adafruit/Adafruit-MiniPOV4-Kit/Bootloader/main.c

/* VUSBtinyBoot by me@frank-zhao.com
 *  
 * VUSBtinyBoot is a bootloader that emulates a USBtinyISP (from Adafruit Industries)
 *  
 * MiniPOV4 (from Adafruit Industries) will use VUSBtinyBoot
 *
 * This code is heavily derived from USBaspLoader, but also from USBtiny, with USBtinyISP's settings
 
   Copyright (c) 2013 Adafruit Industries
   All rights reserved.

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
    THIS SOFTWARE IS PROVIDED BY THE COPYRIGHT HOLDERS AND CONTRIBUTORS "AS IS"
    AND ANY EXPRESS OR IMPLIED WARRANTIES, INCLUDING, BUT NOT LIMITED TO, THE
    IMPLIED WARRANTIES OF MERCHANTABILITY AND FITNESS FOR A PARTICULAR PURPOSE
    ARE DISCLAIMED. IN NO EVENT SHALL THE COPYRIGHT OWNER OR CONTRIBUTORS BE
    LIABLE FOR ANY DIRECT, INDIRECT, INCIDENTAL, SPECIAL, EXEMPLARY, OR
    CONSEQUENTIAL DAMAGES (INCLUDING, BUT NOT LIMITED TO, PROCUREMENT OF
    SUBSTITUTE GOODS OR SERVICES; LOSS OF USE, DATA, OR PROFITS; OR BUSINESS
    INTERRUPTION) HOWEVER CAUSED AND ON ANY THEORY OF LIABILITY, WHETHER IN
    CONTRACT, STRICT LIABILITY, OR TORT (INCLUDING NEGLIGENCE OR OTHERWISE)
    ARISING IN ANY WAY OUT OF THE USE OF THIS SOFTWARE, EVEN IF ADVISED OF THE
    POSSIBILITY OF SUCH DAMAGE.
 */

#include <avr/io.h>
#ifndef MCUSR
#define MCUSR MCUCSR // hack for enabling ATmega8 support
#endif
#define	SIGRD	5	// this is missing from some of the io.h files, this is a hack so avr/boot.h can be used
#include <avr/boot.h>
#include <avr/pgmspace.h>
//#include <avr/fuse.h>
#include <avr/interrupt.h>
#include <avr/wdt.h>
//#include <util/delay.h>
#include <bootloaderconfig.h>
#include <usbdrv/usbdrv.c>	// must be included, because of static function declarations are being used, which saves flash space

// enable features here
#define ENABLE_FLASH_WRITING
#define ENABLE_FLASH_READING
#define ENABLE_EEPROM_WRITING
#define ENABLE_EEPROM_READING
#define ENABLE_SIG_READING
//#define ENABLE_FUSE_READING
#define ENABLE_REQUEST_EXIT // note: enabling this actually decreases code size
#define ENABLE_CLEAN_EXIT // must be used with ENABLE_REQUEST_EXIT

enum
{
	// Generic requests
	USBTINY_ECHO,		// echo test
	USBTINY_READ,		// read byte
	USBTINY_WRITE,		// write byte
	USBTINY_CLR,		// clear bit 
	USBTINY_SET,		// set bit
	// Programming requests
	USBTINY_POWERUP,	// apply power (wValue:SCK-period, wIndex:RESET)
	USBTINY_POWERDOWN,	// remove power from chip
	USBTINY_SPI,		// issue SPI command (wValue:c1c0, wIndex:c3c2)
	USBTINY_POLL_BYTES,	// set poll bytes for write (wValue:p1p2)
	USBTINY_FLASH_READ,	// read flash (wIndex:address)
	USBTINY_FLASH_WRITE,	// write flash (wIndex:address, wValue:timeout)
	USBTINY_EEPROM_READ,	// read eeprom (wIndex:address)
	USBTINY_EEPROM_WRITE,	// write eeprom (wIndex:address, wValue:timeout)
	USBTINY_DDRWRITE,		// set port direction
	USBTINY_SPI1			// a single SPI command
};

#if (FLASHEND) > 0xFFFF		// need long addressing for large flash
#	define CUR_ADDR			cur_addr.addr
#	define addr_t			uint32_t
#else
#	define CUR_ADDR			cur_addr.u16[0]
#	define addr_t			uint16_t
#endif

typedef union longConverter { // utility for manipulating address pointer with proper endianness
	addr_t		addr;
	uint16_t	u16[sizeof(addr_t)/2];
	uint8_t		u8[sizeof(addr_t)];
} longConverter_t;

#ifdef ENABLE_REQUEST_EXIT
static	uint8_t				req_boot_exit;
#endif
static	longConverter_t		cur_addr;
static	uchar				dirty = 0;			// if flash needs to be written
static	uchar				cmd0;				// current read/write command byte
static	uint8_t				remaining;			// bytes remaining in current transaction
static	uchar				buffer[8];			// talk via setup
volatile char				usbHasRxed = 0;		// whether or not USB comm is active

void (*app_start)(void) = 0x0000; // function at start of flash memory, call to exit bootloader

// ----------------------------------------------------------------------
// finishes a write operation if already started
// ----------------------------------------------------------------------
static void finalize_flash_if_dirty()
{
	if (dirty != 0)
	{
		#ifdef ENABLE_FLASH_WRITING
		cli();
		boot_page_write(CUR_ADDR - 2);
		sei();
		boot_spm_busy_wait();
		cli();
		boot_rww_enable();
		sei();
		#endif
		dirty = 0;
	}
}

// ----------------------------------------------------------------------
// Handle a non-standard SETUP packet.
// ----------------------------------------------------------------------
uchar	usbFunctionSetup ( uchar data[8] )
{
	uchar	req;
	usbRequest_t *rq = (void *)data;

	// Generic requests
	req = data[1];
	if ( req == USBTINY_ECHO )
	{
		//usbMsgPtr = data;
		return 8;
	}
	/*
	else if ( req == USBTINY_SET || req == USBTINY_CLR || req == USBTINY_WRITE || req == USBTINY_DDRWRITE || req == USBTINY_POWERUP) {
		// do nothing
		return 0;
	}
	//*/
	else if ( req == USBTINY_READ) {
		// do nothing
		return 1;
	}
	else if ( req == USBTINY_POWERDOWN )
	{
		finalize_flash_if_dirty();
		#ifdef ENABLE_REQUEST_EXIT
		req_boot_exit = 1;
		#endif
		return 0;
	}
	else if ( req == USBTINY_SPI )
	{
		finalize_flash_if_dirty(); // partial page writes are not fully written unless this is called here, it must be HERE

		usbMsgPtr = (usbMsgPtr_t)buffer;

		// this tricks "usbtiny_cmd" into succeeding
		buffer[2] = data[3];

		// for the commands, refer to ATmega datasheet under "Serial Programming Instruction Set"
		// usage of avr/boot.h here is experimental

		#ifdef ENABLE_SIG_READING
		if (data[2] == 0x30 && data[3] == 0x00) {
			// read signature byte
			buffer[3] = boot_signature_byte_get(data[4] * 2);
		}
		#ifndef ENABLE_FUSE_READING
		else
		{
			buffer[3] = 0;
		}
		#endif
		#endif
		#ifdef ENABLE_FUSE_READING
		if (data[2] == 0x50 && data[3] == 0x00 && data[4] == 0x00) {
			// read LFUSE
			buffer[3] = boot_lock_fuse_bits_get(GET_LOW_FUSE_BITS);
		}
		else if (data[2] == 0x58 && data[3] == 0x08 && data[4] == 0x00) {
			// read HFUSE
			buffer[3] = boot_lock_fuse_bits_get(GET_HIGH_FUSE_BITS);
		}
		else if (data[2] == 0x50 && data[3] == 0x08 && data[4] == 0x00) {
			// read EFUSE
			buffer[3] = boot_lock_fuse_bits_get(GET_EXTENDED_FUSE_BITS);
		}
		else if (data[2] == 0x58 && data[3] == 0x00 && data[4] == 0x00) {
			// read lock bits
			buffer[3] = boot_lock_fuse_bits_get(GET_LOCK_BITS);
		}
		else if (data[2] == 0x38 && data[3] == 0x00 && data[4] == 0x00) {
			// read calibration
			buffer[3] = boot_signature_byte_get(0);
		}
		#endif
		#if !defined(ENABLE_SIG_READING) && !defined(ENABLE_FUSE_READING)
		buffer[3] = 0;
		#endif

		// all other commands are unhandled

		return 4;
	}
	else if ( req == USBTINY_SPI1 )
	{
		// I don't know what this is used for, there are no single SPI transactions in the ISP protocol
		finalize_flash_if_dirty();
		return 1;
	}
	else if ( req == USBTINY_POLL_BYTES )
	{
		finalize_flash_if_dirty();
		return 0;
	}
	CUR_ADDR = *((uint16_t*)(&data[4]));
	remaining = rq->wLength.bytes[0];
	if ( req >= USBTINY_FLASH_READ && req <= USBTINY_EEPROM_WRITE )
	{
		cmd0 = req;
		if ( cmd0 != USBTINY_FLASH_WRITE ) {
			finalize_flash_if_dirty();
		}
		return USB_NO_MSG;	// usbFunctionRead() or usbFunctionWrite() will be called to handle the data
	}

	// do nothing if nothing done
	return 0;
}

// ----------------------------------------------------------------------
// Handle an IN packet.
// ----------------------------------------------------------------------
uchar	usbFunctionRead ( uchar* data, uchar len )
{
	uchar	i;

	if(len > remaining) {
		len = remaining;
	}

	remaining -= len;

	for	( i = 0; i < len; i++ )
	{
		if (cmd0 == USBTINY_EEPROM_READ) {
			#ifdef ENABLE_EEPROM_READING
			*data = eeprom_read_byte((void *)cur_addr.u16[0]);
			#endif
		}
		else if (cmd0 == USBTINY_FLASH_READ) {
			#ifdef ENABLE_FLASH_READING
			*data = pgm_read_byte((void *)CUR_ADDR);
			#endif
		}
		data++;
		CUR_ADDR++;
	}
	return len;
}

// ----------------------------------------------------------------------
// Handle an OUT packet.
// ----------------------------------------------------------------------
uchar	usbFunctionWrite ( uchar* data, uchar len )
{
	uchar	i, isLast;

	if(len > remaining) {
		len = remaining;
	}
	remaining -= len;
	isLast = remaining == 0;

	if (cmd0 == USBTINY_EEPROM_WRITE)
	{
		#ifdef ENABLE_EEPROM_WRITING
		for	( i = 0; i < len; i++ ) {
			eeprom_write_byte((void *)(cur_addr.u16[0]++), *data++);
		}
		#endif
	}
	else if (cmd0 == USBTINY_FLASH_WRITE)
	{
		#ifdef ENABLE_FLASH_WRITING
		for ( i = 0; i < len; )
		{
			if ((cur_addr.u16[0] & (SPM_PAGESIZE - 1)) == 0) {
				// page start, erase
				cli();
				boot_page_erase(CUR_ADDR);
				sei();
				boot_spm_busy_wait();
			}

			dirty = 1;
			cli();
			boot_page_fill(CUR_ADDR, *(short *)data);
			sei();

			CUR_ADDR += 2;
			data += 2;
			i += 2;

			if ((cur_addr.u16[0] & (SPM_PAGESIZE - 1)) == 0) {
				// end of page
				finalize_flash_if_dirty();
			}
		}
		#endif
	}

	return isLast;
}

// ----------------------------------------------------------------------
// Bootloader main entry point
// ----------------------------------------------------------------------
int	main ( void )
{
	// disable watchdog if previously enabled
	MCUSR &= ~(1 << WDRF);
	wdt_disable();

	MCUCR = (1 << IVCE);	// enable change of interrupt vectors
	MCUCR = (1 << IVSEL);	// move interrupts to boot flash section

	// start 16-bit timer1
	TCCR1B = 0x05;

	// start USB and force a re-enumeration by faking a disconnect
	usbInit();
	usbDeviceDisconnect();
	while (TCNT1 < 3000);
	usbDeviceConnect();
	sei();

	// make LED output
	DDRB |= _BV(5);
	PORTB |= _BV(5);

	// main program loop
	while (1)
	{
		usbPoll();

		if ((usbHasRxed == 0 && TCNT1 >= 0x8900)
		#ifdef ENABLE_REQUEST_EXIT
		|| req_boot_exit != 0
		#endif
		) {
			// requested exit
			// or timed out waiting for activity (timeout means not connected to computer)
			break;
		}
	}

	#if defined(ENABLE_REQUEST_EXIT) && defined(ENABLE_CLEAN_EXIT)
	// wait to finish all USB comms, avoids "avrdude: error: usbtiny_transmit: usb_control_msg: sending control message failed"
	TCNT1 = 0; while (req_boot_exit != 0 && TCNT1 < 3000) usbPoll();
	#endif

	// cleanup!

	// reset timer
	TCCR1B = 0;
	TCNT1 = 0;

	// deinitialize USB
	USB_INTR_ENABLE = 0;
	USB_INTR_CFG = 0;

	// move interrupt back
	MCUCR = (1 << IVCE);	// enable change of interrupt vectors
	MCUCR = (0 << IVSEL);	// move interrupts to app flash section

	// make LED input
	DDRB &= ~_BV(5);
	PORTB &= ~_BV(5);

	cli();// disable interrupts

	app_start(); // jump to user app

	return 0;
}
